Pelicram/Hattara-Printable-Low-Profile-Keycaps/Choc Keycaps/Choc Spacing/STEP/Raw Caps/Choc-cs-homing-bar-bottom.step

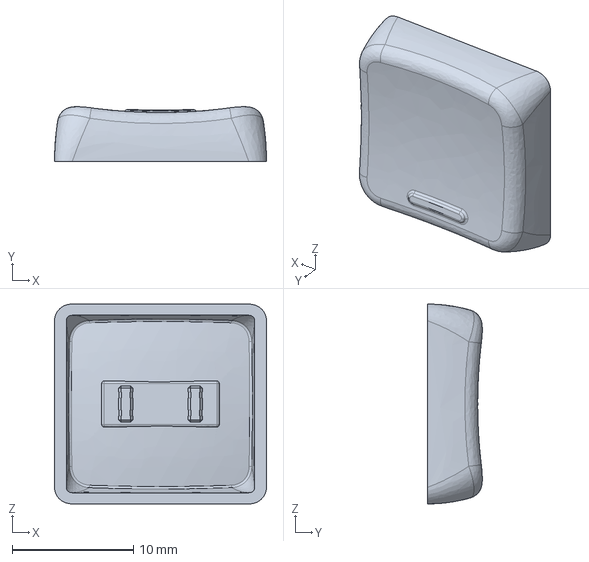
[picture p19: CAD file, 2022-11-11]
Choc Keycaps/Choc Spacing/STEP/Raw Caps/Choc-cs-homing-bar-bottom.step
17.5 x 4.50 x 16.5 mm
