Pelicram/Hattara-Printable-Low-Profile-Keycaps/Choc Keycaps/MX Spacing/STEP/Sprues/Choc-mxs-1u-sprue.step

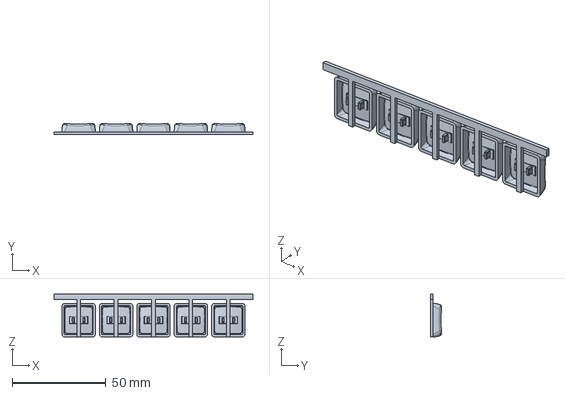
[picture p20: CAD file, 2022-11-11]
Choc Keycaps/MX Spacing/STEP/Sprues/Choc-mxs-1u-sprue.step
106.4 x 5.98 x 22.9 mm
