Pelicram/Hattara-Printable-Low-Profile-Keycaps/MX Keycaps/STEP/Sprues/MX-iso-sprue.step

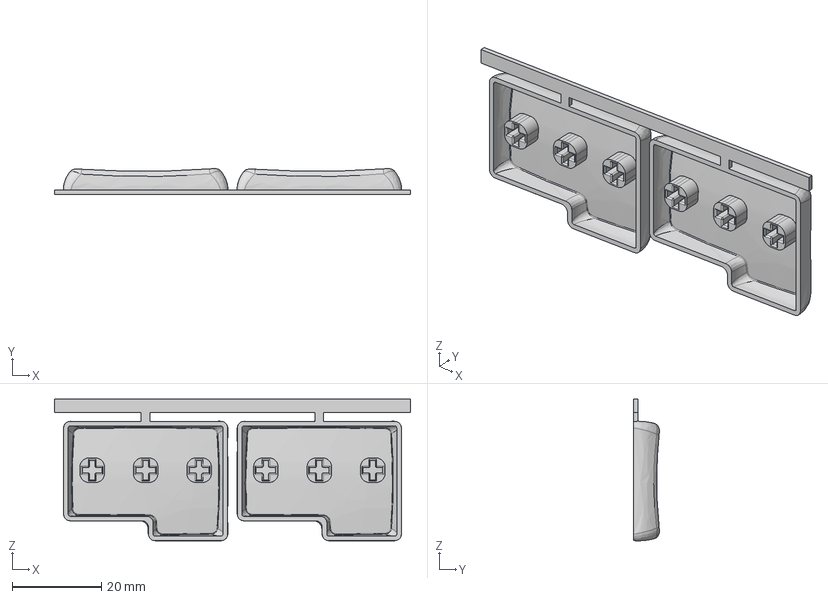
[picture p21: CAD file, 2022-11-11]
MX Keycaps/STEP/Sprues/MX-iso-sprue.step
79.9 x 5.77 x 31.8 mm
