Pelicram/Hattara-Printable-Low-Profile-Keycaps/Choc Keycaps/Choc Spacing/STEP/Raw Caps/Choc-cs-homing-bar-center.step

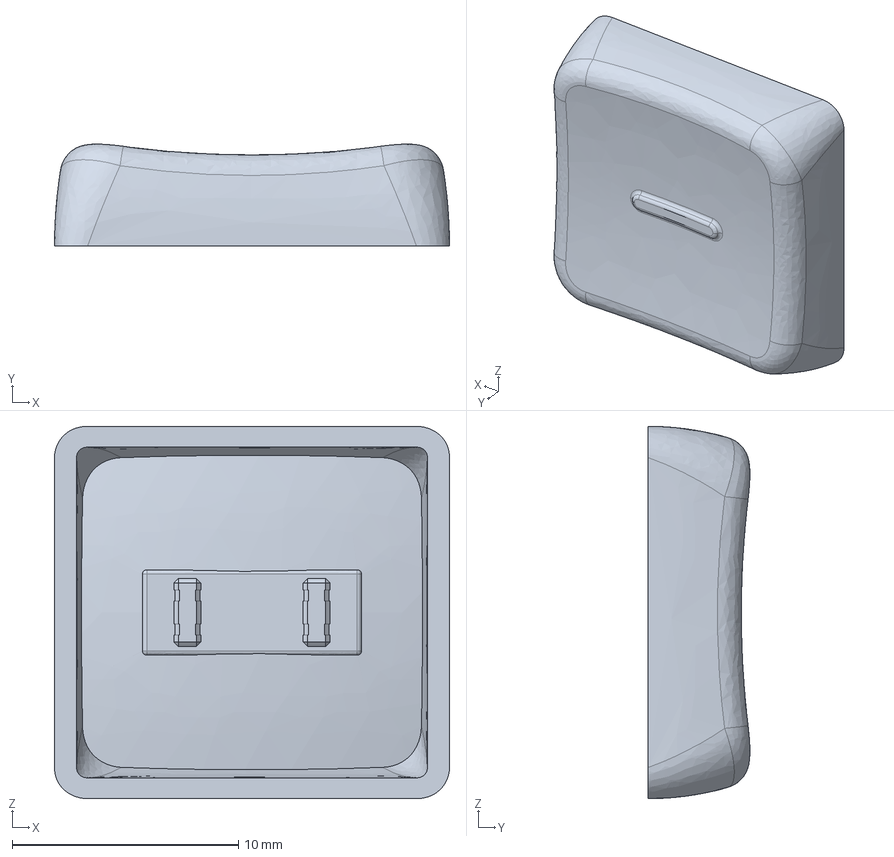
[picture p22: CAD file, 2022-11-11]
Choc Keycaps/Choc Spacing/STEP/Raw Caps/Choc-cs-homing-bar-center.step
17.5 x 4.50 x 16.5 mm
