Pelicram/Hattara-Printable-Low-Profile-Keycaps/Choc Keycaps/Choc Spacing/STEP/Sprues/Choc-cs-1_25u-sprue.step

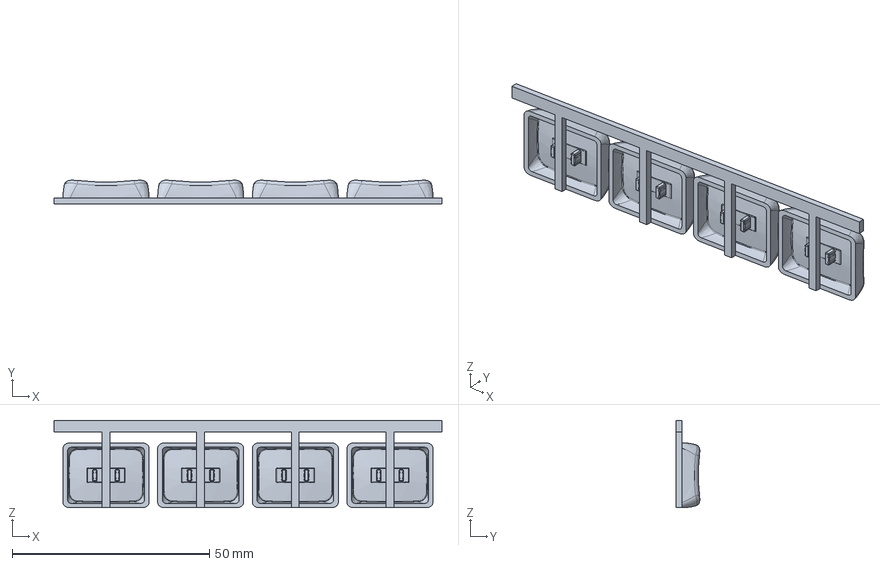
[picture p23: CAD file, 2022-11-11]
Choc Keycaps/Choc Spacing/STEP/Sprues/Choc-cs-1_25u-sprue.step
98.4 x 5.98 x 22.2 mm
