Pelicram/Hattara-Printable-Low-Profile-Keycaps/Choc Keycaps/MX Spacing/STEP/Sprues/Choc-mxs-homing-bumps-sprue.step

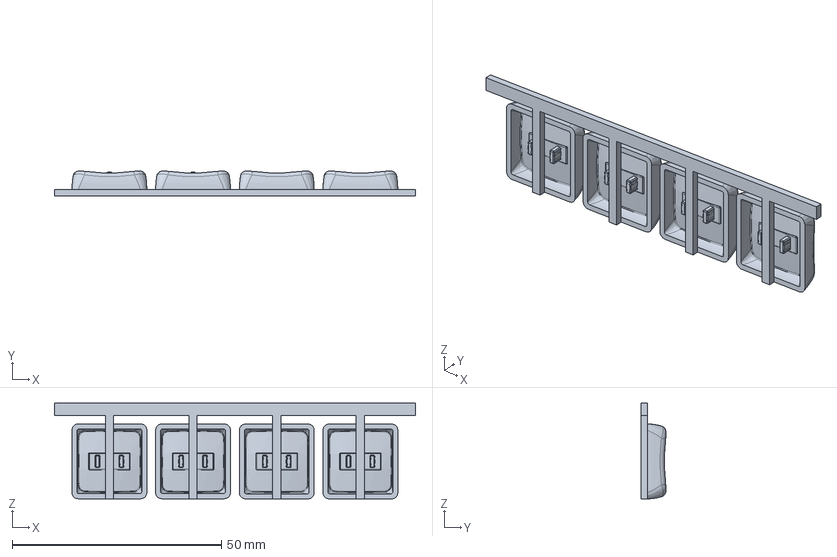
[picture p24: CAD file, 2022-11-11]
Choc Keycaps/MX Spacing/STEP/Sprues/Choc-mxs-homing-bumps-sprue.step
86.4 x 5.98 x 22.9 mm
