Pelicram/Hattara-Printable-Low-Profile-Keycaps/MX Keycaps/STEP/Sprues/MX-1_5u-sprue.step

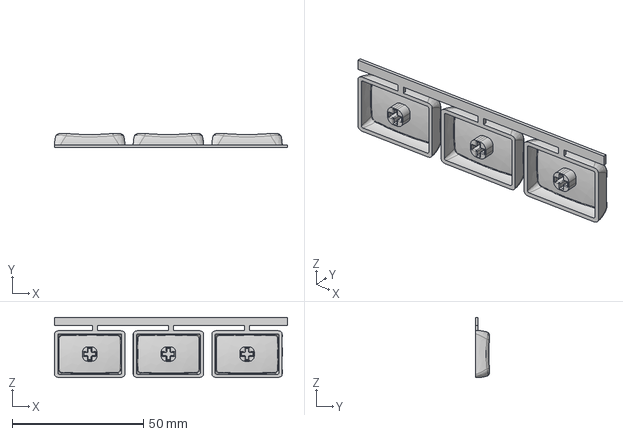
[picture p25: CAD file, 2022-11-11]
MX Keycaps/STEP/Sprues/MX-1_5u-sprue.step
88.8 x 5.48 x 22.9 mm
