Pelicram/Hattara-Printable-Low-Profile-Keycaps/Choc Keycaps/Choc Spacing/STEP/Sprues/Choc-cs-1u-sprue.step

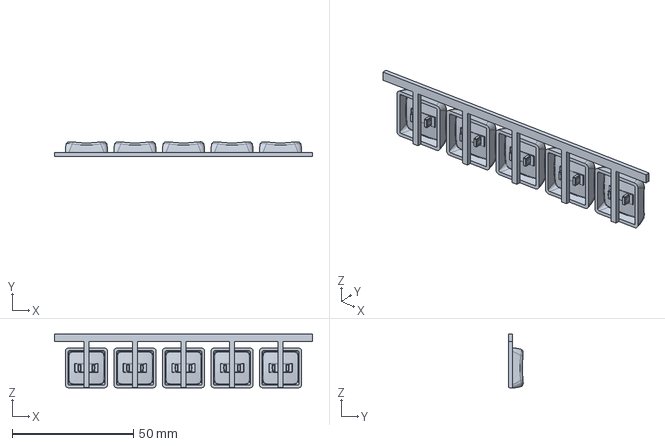
[picture p26: CAD file, 2022-11-11]
Choc Keycaps/Choc Spacing/STEP/Sprues/Choc-cs-1u-sprue.step
106.4 x 5.99 x 22.2 mm
