Pelicram/Hattara-Printable-Low-Profile-Keycaps/Choc Keycaps/MX Spacing/STEP/Sprues/Choc-mxs-1_5u-sprue.step

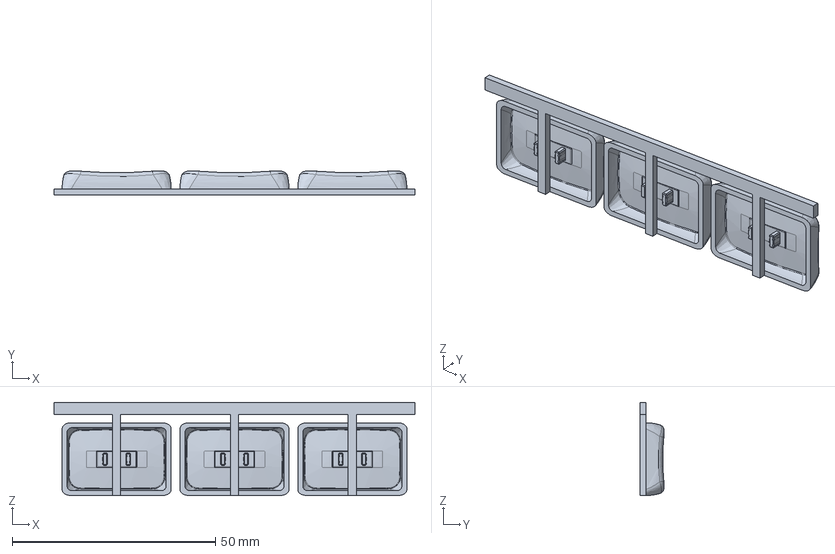
[picture p27: CAD file, 2022-11-11]
Choc Keycaps/MX Spacing/STEP/Sprues/Choc-mxs-1_5u-sprue.step
88.8 x 5.98 x 22.9 mm
