Pelicram/Hattara-Printable-Low-Profile-Keycaps/MX Keycaps/STEP/Raw Caps/MX-1_25u.step

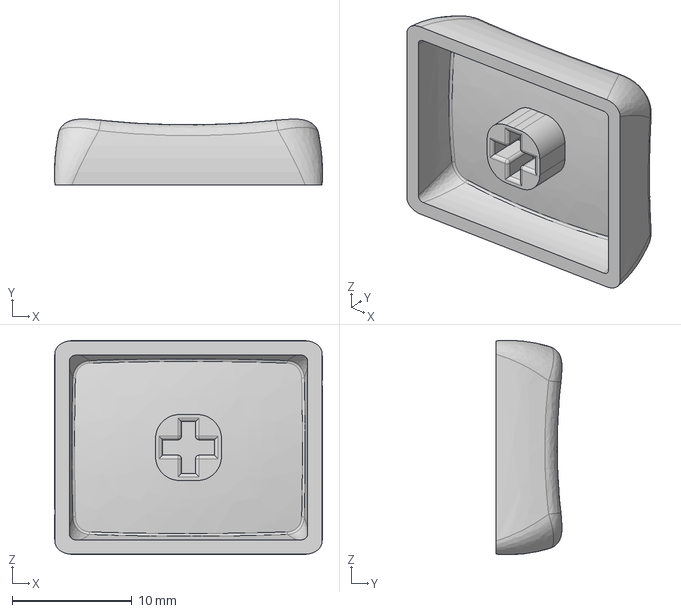
[picture p28: CAD file, 2022-11-11]
MX Keycaps/STEP/Raw Caps/MX-1_25u.step
22.4 x 5.50 x 17.9 mm
