Pelicram/Hattara-Printable-Low-Profile-Keycaps/MX Keycaps/STEP/Sprues/MX-1_25u-sprue.step

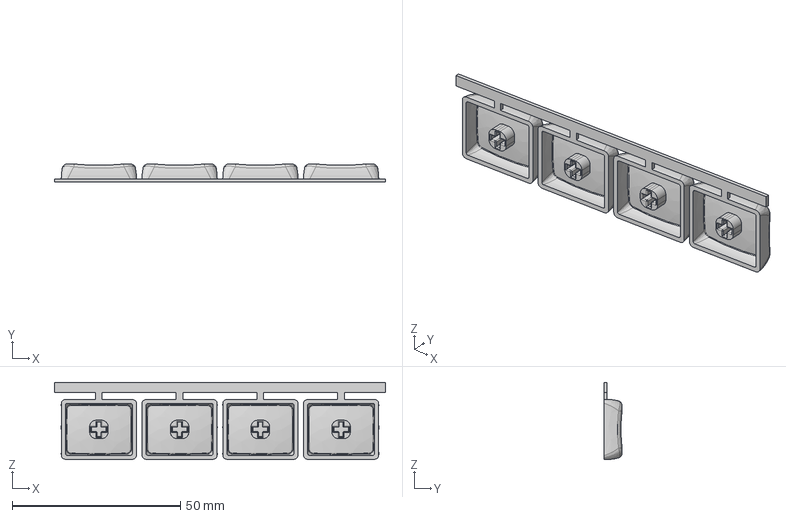
[picture p29: CAD file, 2022-11-11]
MX Keycaps/STEP/Sprues/MX-1_25u-sprue.step
98.4 x 5.48 x 22.9 mm
