Pelicram/Hattara-Printable-Low-Profile-Keycaps/Choc Keycaps/Choc Spacing/STEP/Raw Caps/Choc-cs-1_5u.step

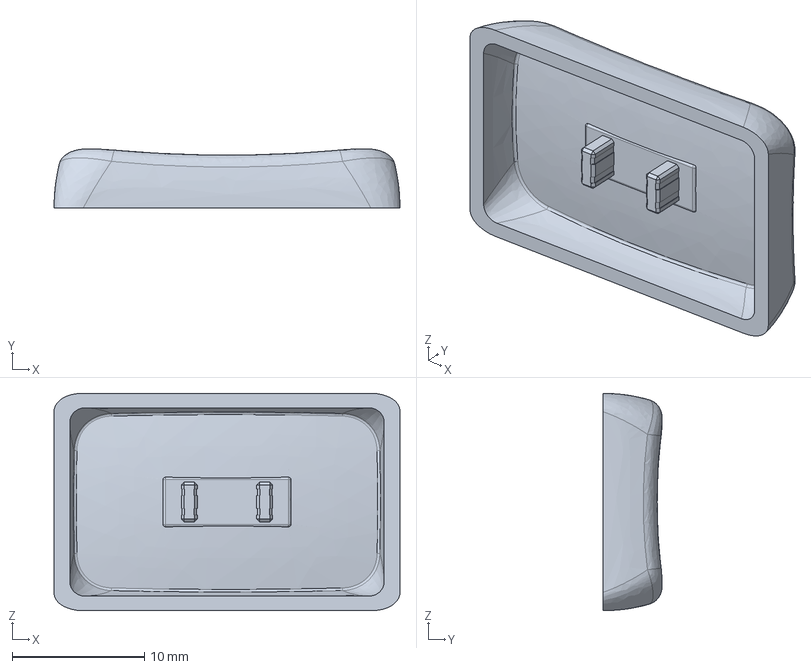
[picture p30: CAD file, 2022-11-11]
Choc Keycaps/Choc Spacing/STEP/Raw Caps/Choc-cs-1_5u.step
26.2 x 4.50 x 16.5 mm
