Pelicram/Hattara-Printable-Low-Profile-Keycaps/Choc Keycaps/MX Spacing/STEP/Sprues/Choc-mxs-1_25u-sprue.step

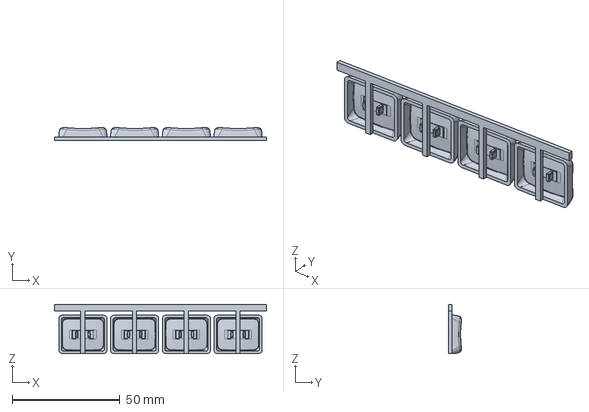
[picture p31: CAD file, 2022-11-11]
Choc Keycaps/MX Spacing/STEP/Sprues/Choc-mxs-1_25u-sprue.step
98.4 x 5.98 x 22.9 mm
