Pelicram/Hattara-Printable-Low-Profile-Keycaps/MX Keycaps/STEP/Raw Caps/MX-iso.step

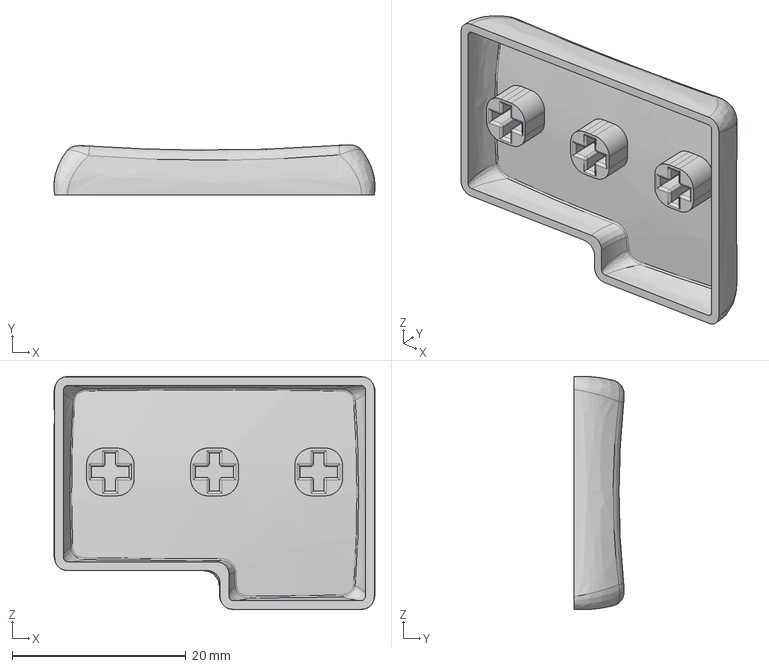
[picture p32: CAD file, 2022-11-11]
MX Keycaps/STEP/Raw Caps/MX-iso.step
37.0 x 5.77 x 26.8 mm
