Pelicram/Hattara-Printable-Low-Profile-Keycaps/MX Keycaps/STEP/Sprues/MX-homing-scoops-sprue.step

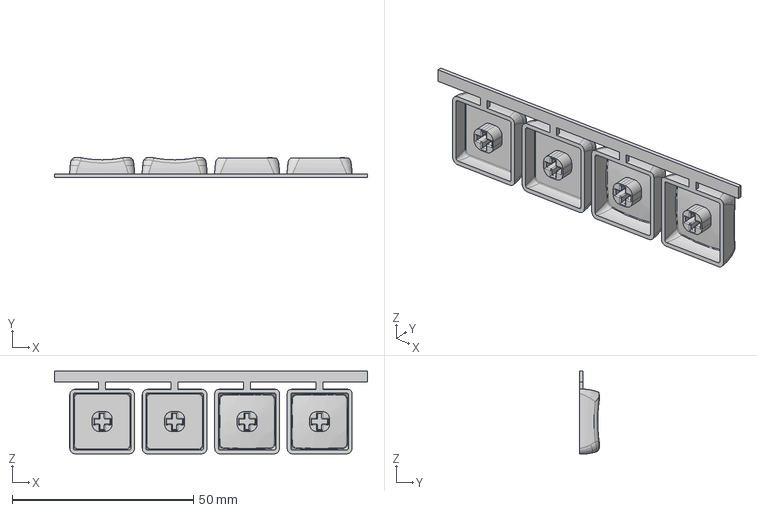
[picture p33: CAD file, 2022-11-11]
MX Keycaps/STEP/Sprues/MX-homing-scoops-sprue.step
86.4 x 5.62 x 22.9 mm
