Pelicram/Hattara-Printable-Low-Profile-Keycaps/Choc Keycaps/MX Spacing/STEP/Raw Caps/Choc-mxs-homing-scoop-classic.step

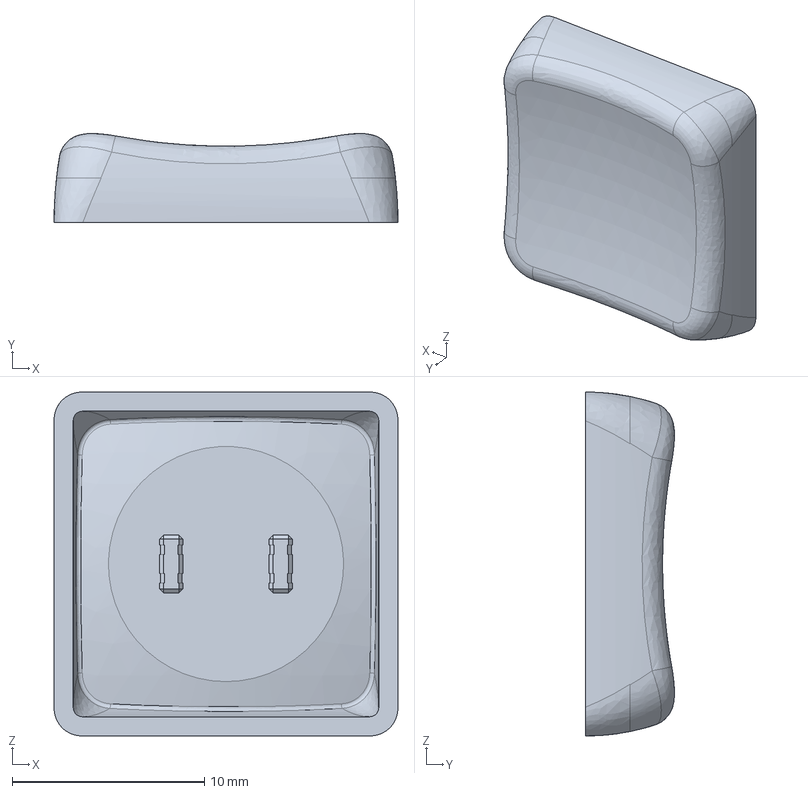
[picture p34: CAD file, 2022-11-11]
Choc Keycaps/MX Spacing/STEP/Raw Caps/Choc-mxs-homing-scoop-classic.step
17.9 x 4.62 x 17.9 mm
