Pelicram/Hattara-Printable-Low-Profile-Keycaps/MX Keycaps/STEP/Raw Caps/MX-homing-scoop-classic.step

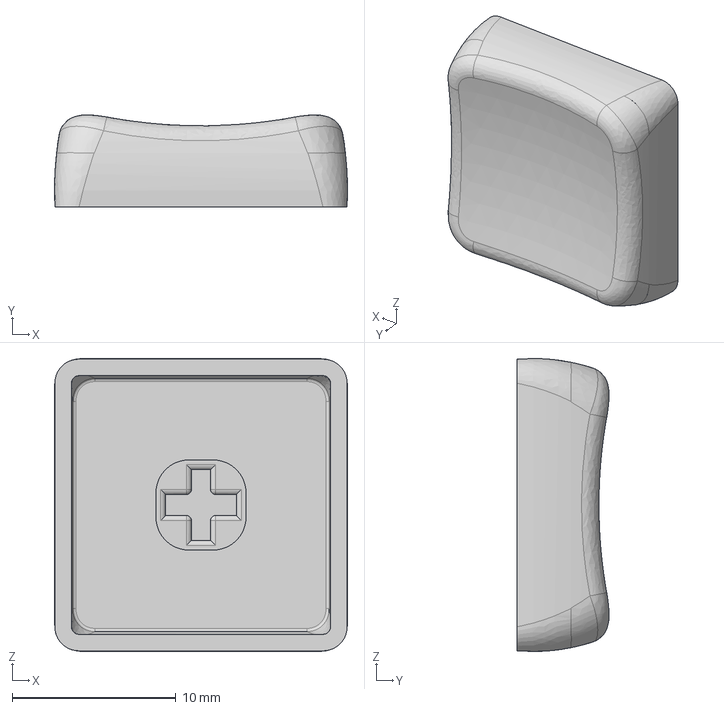
[picture p35: CAD file, 2022-11-11]
MX Keycaps/STEP/Raw Caps/MX-homing-scoop-classic.step
17.9 x 5.63 x 17.9 mm
