Pelicram/Hattara-Printable-Low-Profile-Keycaps/Choc Keycaps/Choc Spacing/STEP/Raw Caps/Choc-cs-1_25u.step

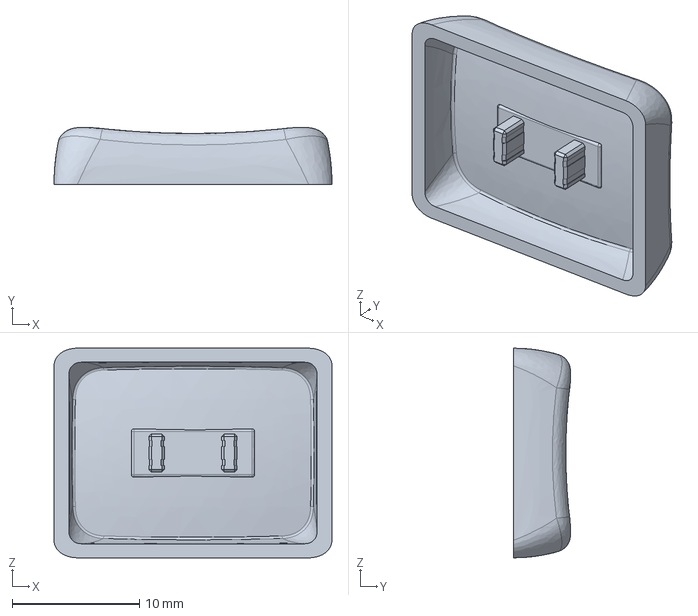
[picture p36: CAD file, 2022-11-11]
Choc Keycaps/Choc Spacing/STEP/Raw Caps/Choc-cs-1_25u.step
21.8 x 4.50 x 16.5 mm
