Pelicram/Hattara-Printable-Low-Profile-Keycaps/Choc Keycaps/MX Spacing/STEP/Raw Caps/Choc-mxs-1_5u.step

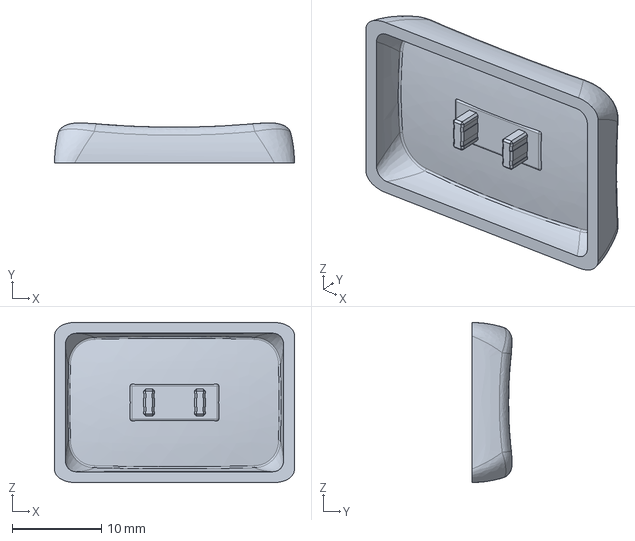
[picture p37: CAD file, 2022-11-11]
Choc Keycaps/MX Spacing/STEP/Raw Caps/Choc-mxs-1_5u.step
26.8 x 4.50 x 17.9 mm
