Pelicram/Hattara-Printable-Low-Profile-Keycaps/MX Keycaps/STEP/Raw Caps/MX-1_5u.step

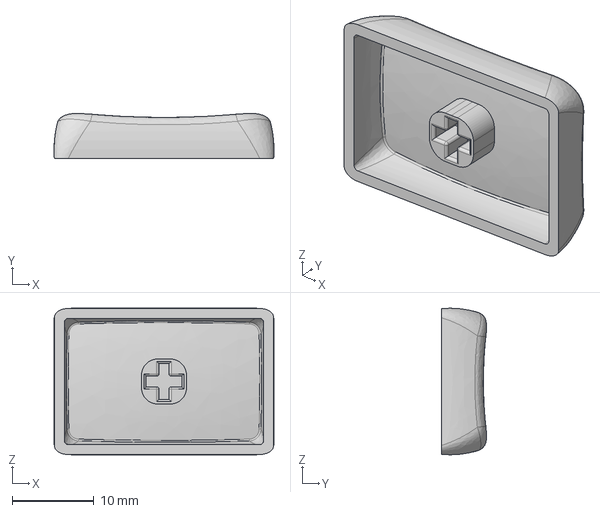
[picture p38: CAD file, 2022-11-11]
MX Keycaps/STEP/Raw Caps/MX-1_5u.step
26.8 x 5.50 x 17.9 mm
